abbvie-external/IR-MALDESI-MS/CAD/ArduinoMega.SLDPRT

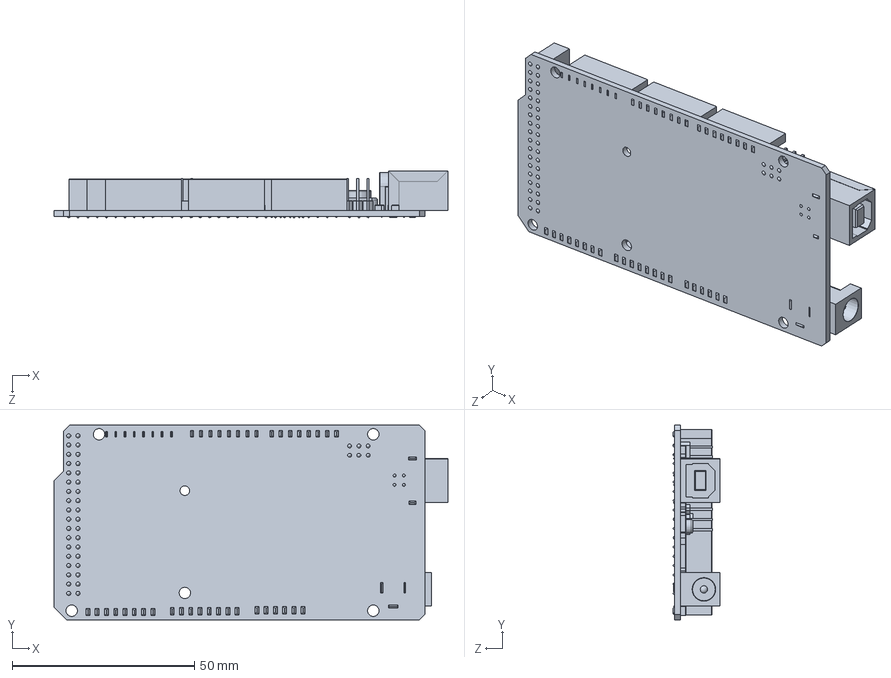
[picture p17: CAD file, 2023-03-30]
CAD/ArduinoMega.SLDPRT
107.9 x 53.4 x 13.0 mm
