abbvie-external/IR-MALDESI-MS/CAD/1332-0086.SLDPRT

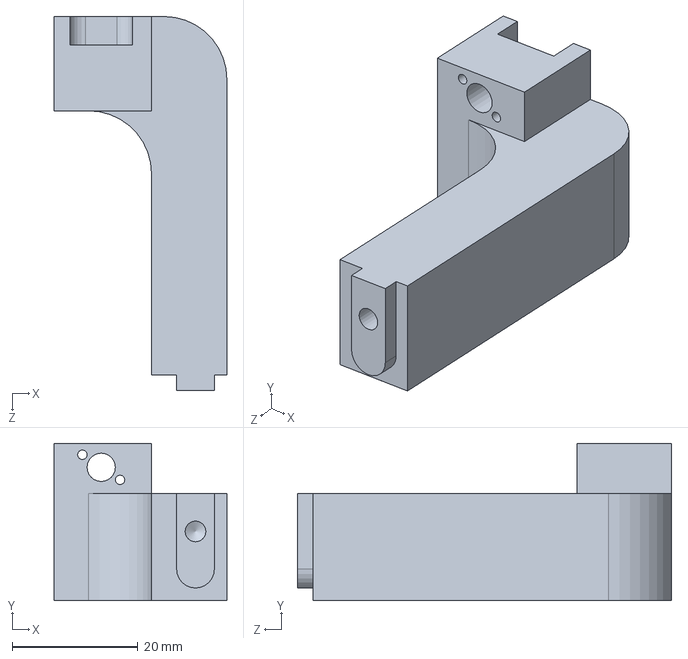
[picture p18: CAD file, 2023-03-30]
CAD/1332-0086.SLDPRT
27.5 x 25.0 x 59.5 mm
