abbvie-external/IR-MALDESI-MS/CAD/Axis 5 Wrist support simple.SLDPRT

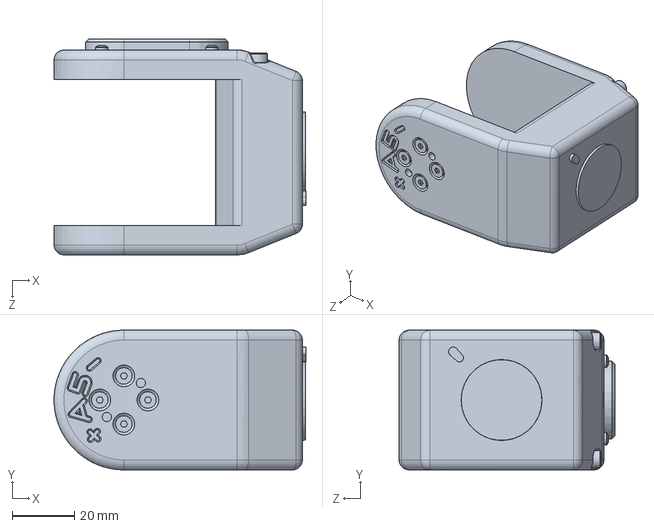
[picture p19: CAD file, 2023-03-30]
CAD/Axis 5 Wrist support simple.SLDPRT
81.1 x 45.0 x 69.5 mm
