abbvie-external/IR-MALDESI-MS/CAD/1332-0083.SLDPRT

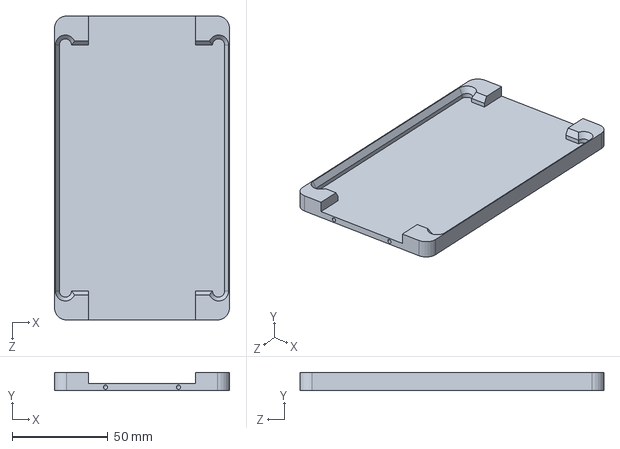
[picture p20: CAD file, 2023-03-30]
CAD/1332-0083.SLDPRT
91.4 x 9.53 x 158.8 mm
