abbvie-external/IR-MALDESI-MS/CAD/1332-0091.SLDPRT

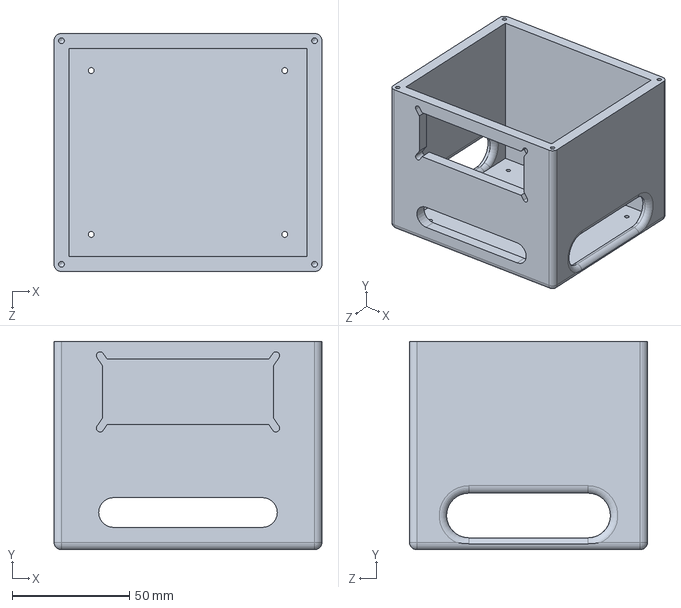
[picture p21: CAD file, 2023-03-30]
CAD/1332-0091.SLDPRT
114.3 x 88.9 x 101.6 mm
