abbvie-external/IR-MALDESI-MS/CAD/1332-0089.SLDPRT

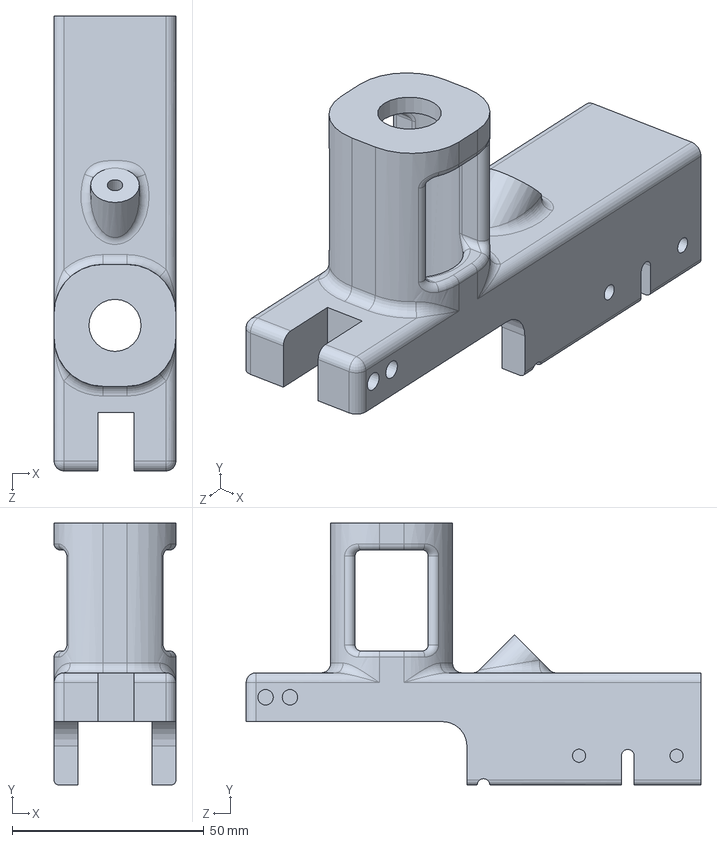
[picture p22: CAD file, 2023-03-30]
CAD/1332-0089.SLDPRT
31.8 x 68.3 x 118.5 mm
