abbvie-external/IR-MALDESI-MS/CAD/SM05V10.SLDPRT

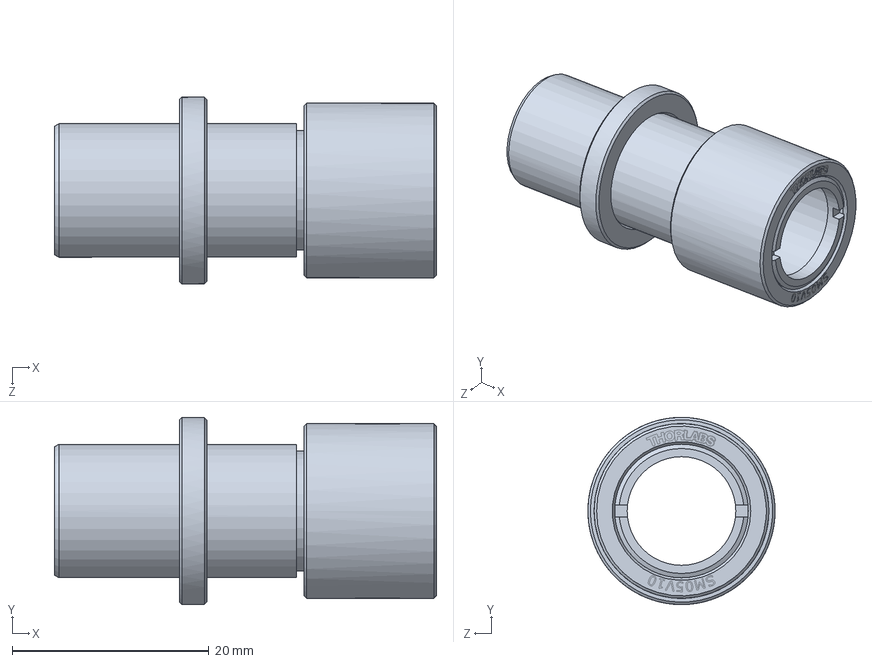
[picture p23: CAD file, 2023-03-30]
CAD/SM05V10.SLDPRT
38.9 x 19.0 x 19.1 mm
