abbvie-external/IR-MALDESI-MS/CAD/Meca Rail adjustable.SLDPRT

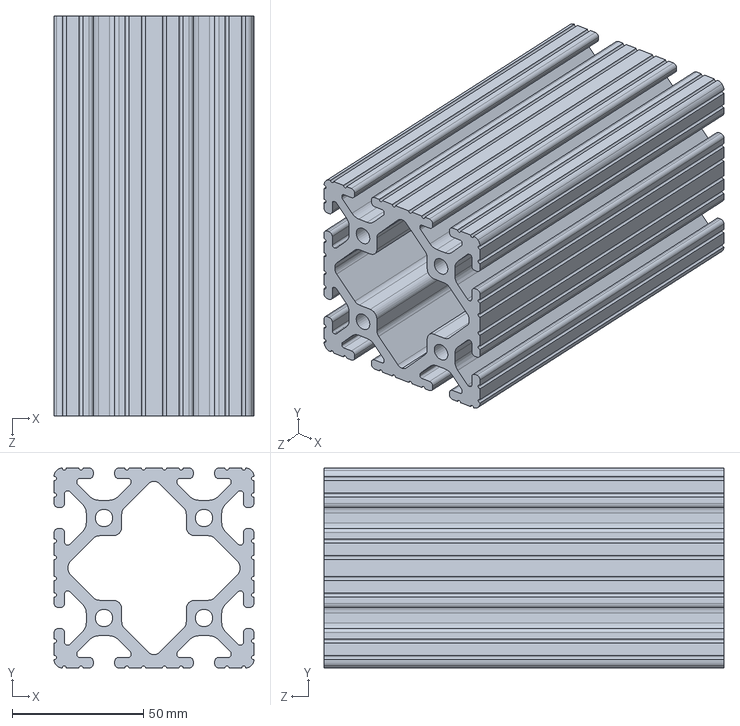
[picture p24: CAD file, 2023-03-30]
CAD/Meca Rail adjustable.SLDPRT
76.2 x 76.2 x 152.4 mm
