abbvie-external/IR-MALDESI-MS/CAD/Thermo Q Exactive HF.SLDPRT

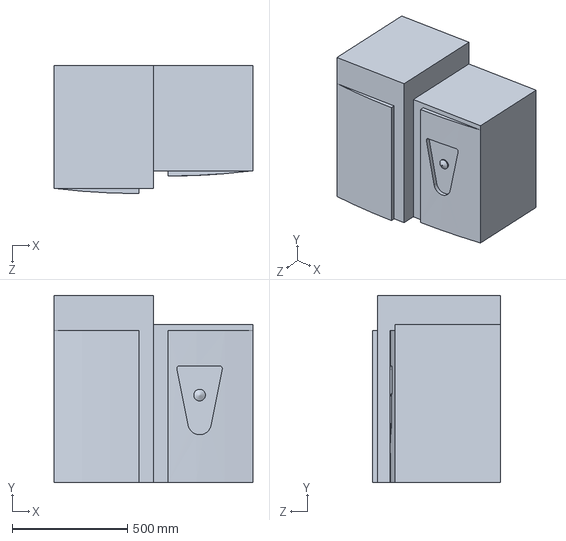
[picture p25: CAD file, 2023-03-30]
CAD/Thermo Q Exactive HF.SLDPRT
863.6 x 812.8 x 556.3 mm
