abbvie-external/IR-MALDESI-MS/CAD/U-MALDESI - Silica ESI Probe.SLDPRT

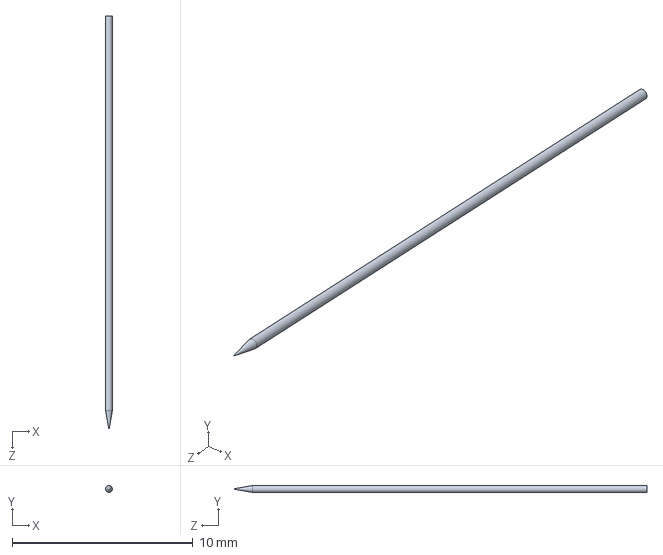
[picture p26: CAD file, 2023-03-30]
CAD/U-MALDESI - Silica ESI Probe.SLDPRT
0.381 x 0.381 x 22.9 mm
