abbvie-external/IR-MALDESI-MS/CAD/1332-0079.SLDPRT

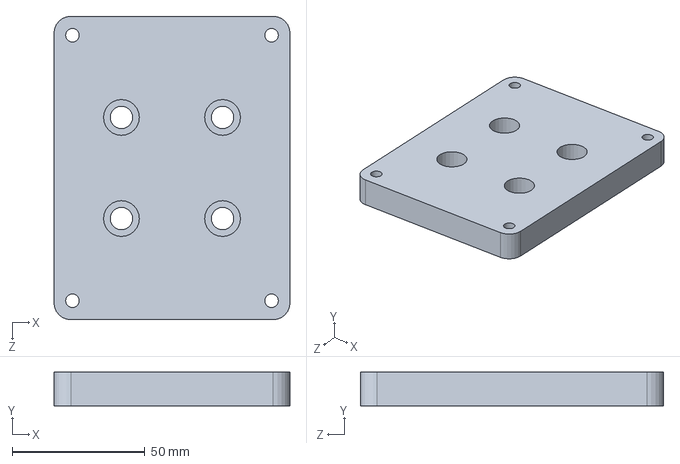
[picture p27: CAD file, 2023-03-30]
CAD/1332-0079.SLDPRT
88.9 x 12.7 x 114.3 mm
