abbvie-external/IR-MALDESI-MS/CAD/KCB05.SLDPRT

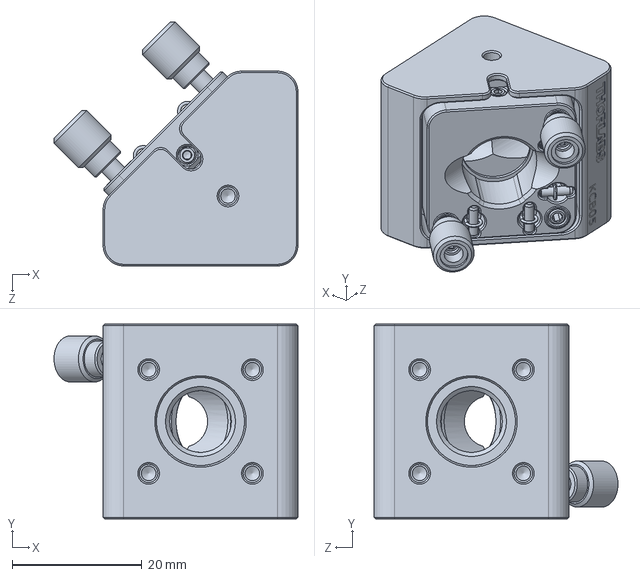
[picture p28: CAD file, 2023-03-30]
CAD/KCB05.SLDPRT
37.6 x 30.1 x 37.6 mm
