abbvie-external/IR-MALDESI-MS/CAD/DIN RAIL 35mm X 7.5mm.SLDPRT

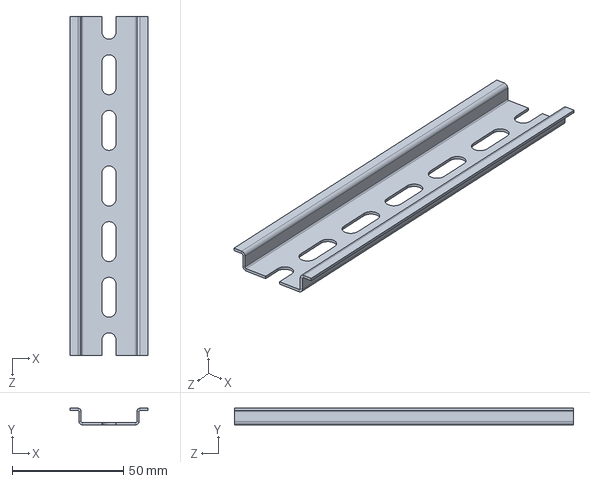
[picture p29: CAD file, 2023-03-30]
CAD/DIN RAIL 35mm X 7.5mm.SLDPRT
35.0 x 7.50 x 152.4 mm
