abbvie-external/IR-MALDESI-MS/CAD/SM05L30.SLDPRT

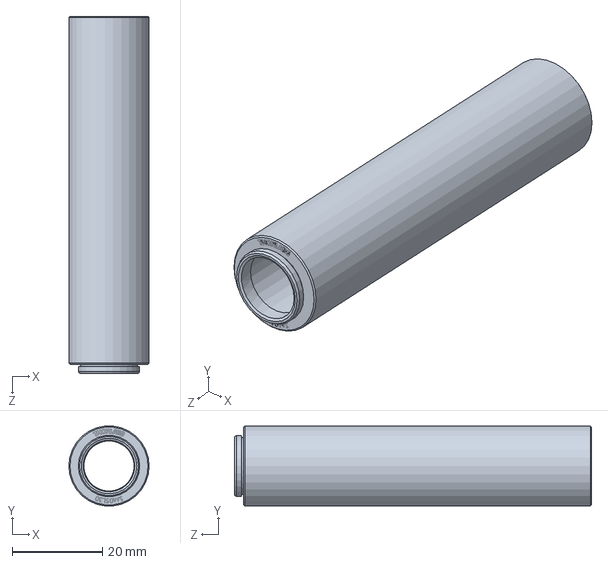
[picture p30: CAD file, 2023-03-30]
CAD/SM05L30.SLDPRT
17.8 x 17.7 x 79.0 mm
