abbvie-external/IR-MALDESI-MS/CAD/Meca500 Power Supply.SLDPRT

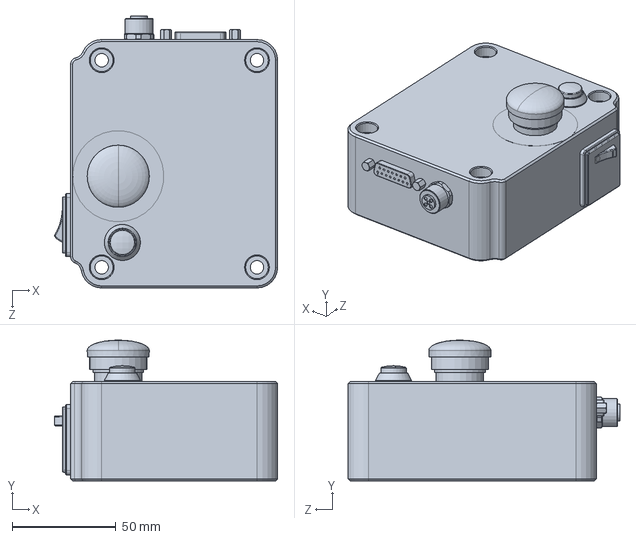
[picture p31: CAD file, 2023-03-30]
CAD/Meca500 Power Supply.SLDPRT
107.9 x 68.0 x 131.4 mm
