abbvie-external/IR-MALDESI-MS/CAD/1332-0093.SLDPRT

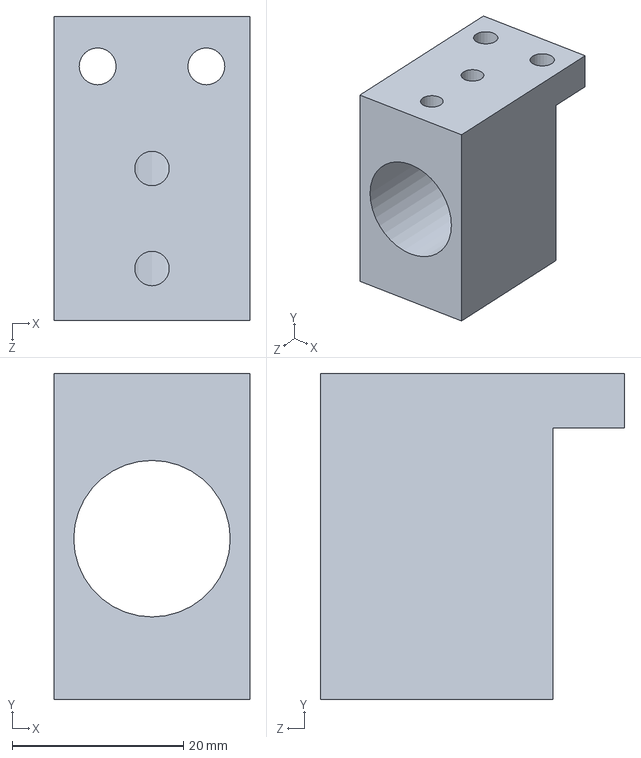
[picture p32: CAD file, 2023-03-30]
CAD/1332-0093.SLDPRT
22.9 x 38.1 x 35.6 mm
