abbvie-external/IR-MALDESI-MS/CAD/1332-0078.SLDPRT

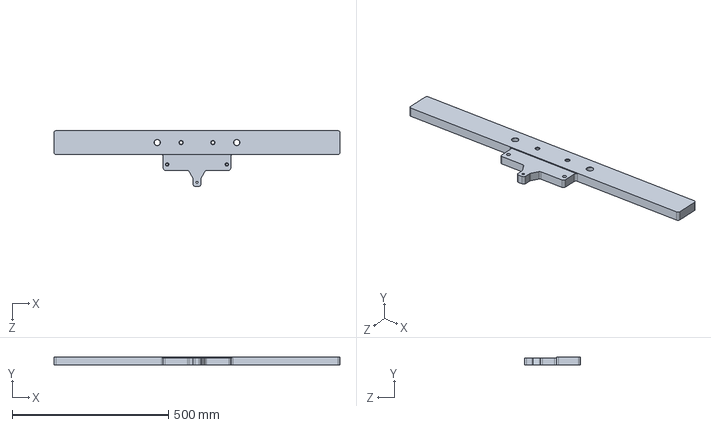
[picture p33: CAD file, 2023-03-30]
CAD/1332-0078.SLDPRT
914.4 x 25.4 x 177.8 mm
