abbvie-external/IR-MALDESI-MS/CAD/Tecan Genesis Workstation 100 - RoMa Gripper SBS Finger LEFT.SLDPRT

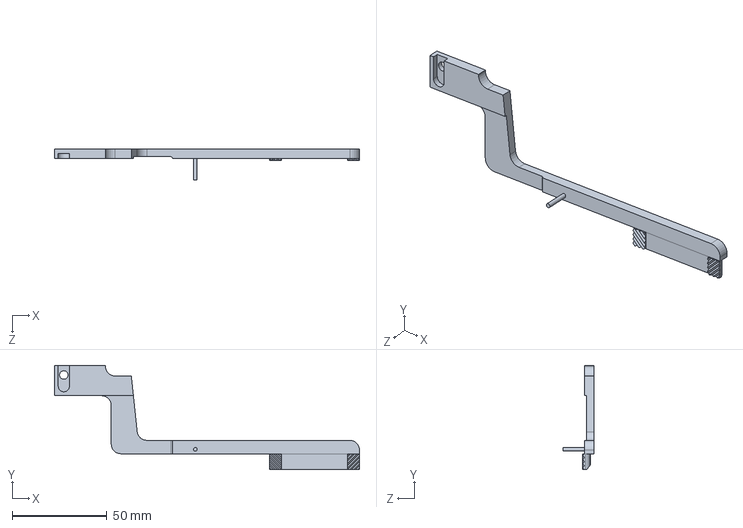
[picture p34: CAD file, 2023-03-30]
CAD/Tecan Genesis Workstation 100 - RoMa Gripper SBS Finger LEFT.SLDPRT
161.3 x 55.1 x 16.2 mm
