abbvie-external/IR-MALDESI-MS/CAD/Tecan Genesis Workstation 100 - RoMa Gripper SBS Finger RIGHT.SLDPRT

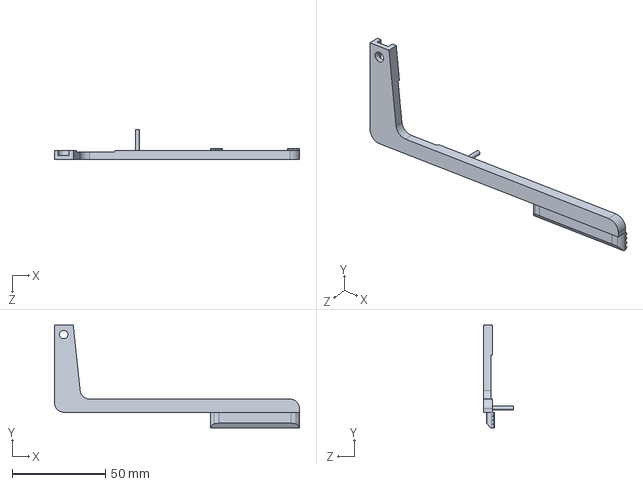
[picture p35: CAD file, 2023-03-30]
CAD/Tecan Genesis Workstation 100 - RoMa Gripper SBS Finger RIGHT.SLDPRT
131.3 x 55.1 x 16.2 mm
