abbvie-external/IR-MALDESI-MS/CAD/Gripper.SLDPRT

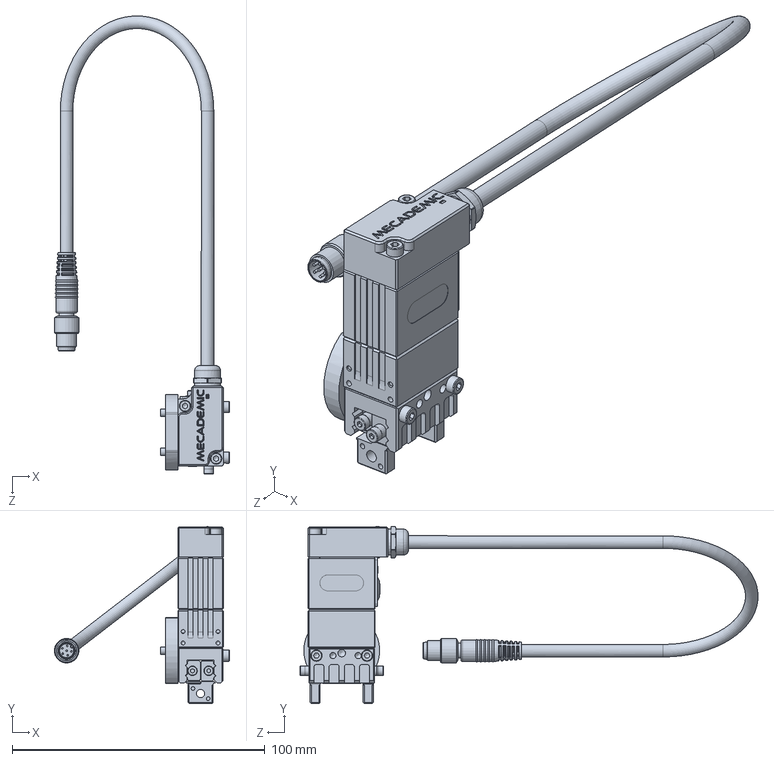
[picture p36: CAD file, 2023-03-30]
CAD/Gripper.SLDPRT
69.2 x 70.1 x 181.1 mm
