abbvie-external/IR-MALDESI-MS/CAD/1332-0081.SLDPRT

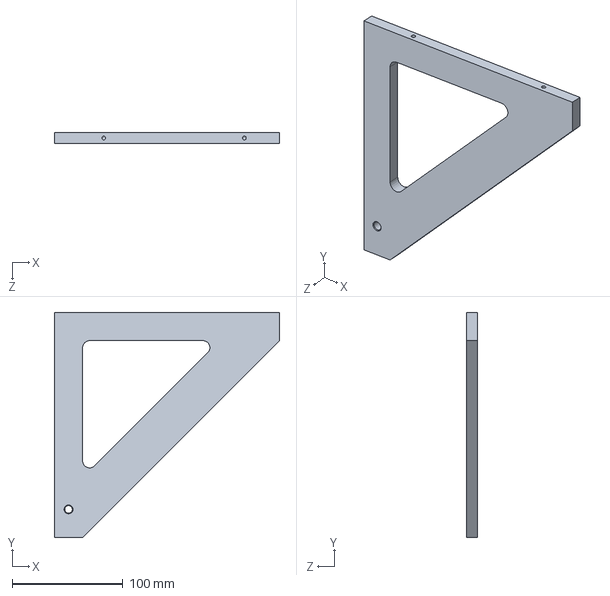
[picture p37: CAD file, 2023-03-30]
CAD/1332-0081.SLDPRT
203.2 x 203.2 x 9.53 mm
