abbvie-external/IR-MALDESI-MS/CAD/1332-0082.SLDPRT

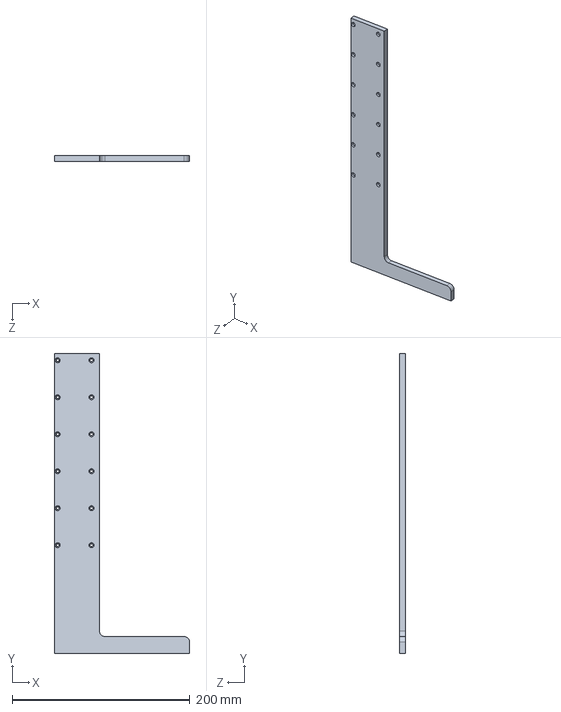
[picture p38: CAD file, 2023-03-30]
CAD/1332-0082.SLDPRT
152.4 x 337.8 x 6.35 mm
