abbvie-external/IR-MALDESI-MS/CAD/Axis 2 Hip support simple.SLDPRT

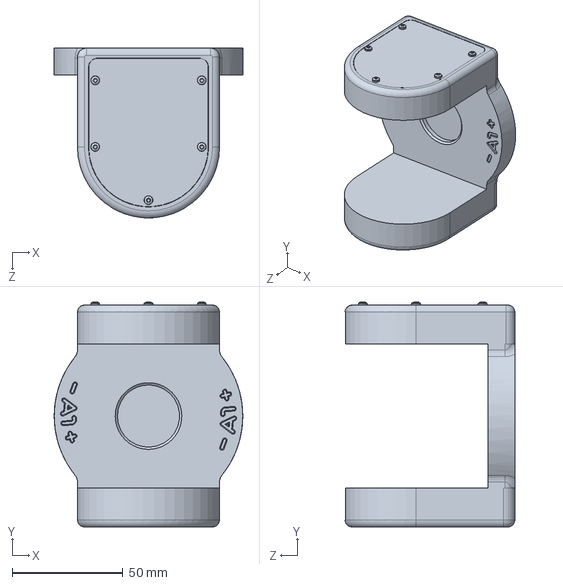
[picture p39: CAD file, 2023-03-30]
CAD/Axis 2 Hip support simple.SLDPRT
85.0 x 101.4 x 76.5 mm
