abbvie-external/IR-MALDESI-MS/CAD/Axis 6 Wrist simple.SLDPRT

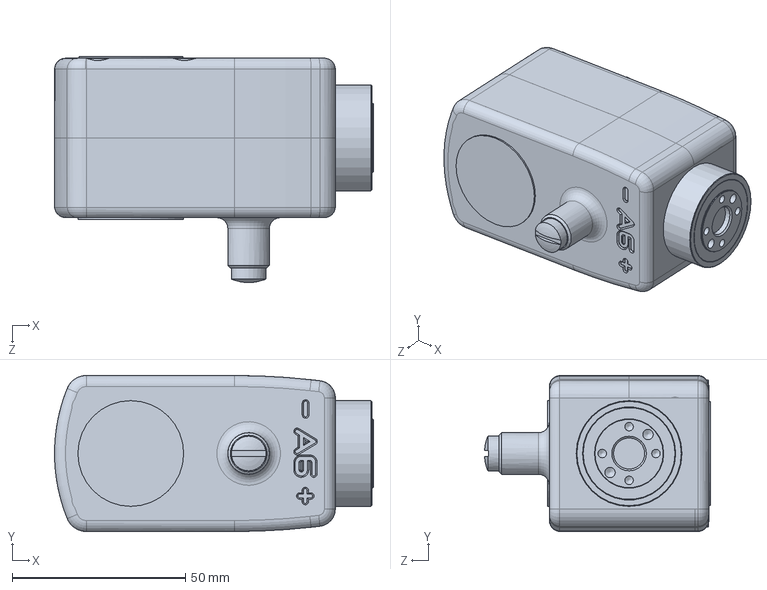
[picture p40: CAD file, 2023-03-30]
CAD/Axis 6 Wrist simple.SLDPRT
92.0 x 45.0 x 65.2 mm
