abbvie-external/IR-MALDESI-MS/CAD/1332-0092.SLDPRT

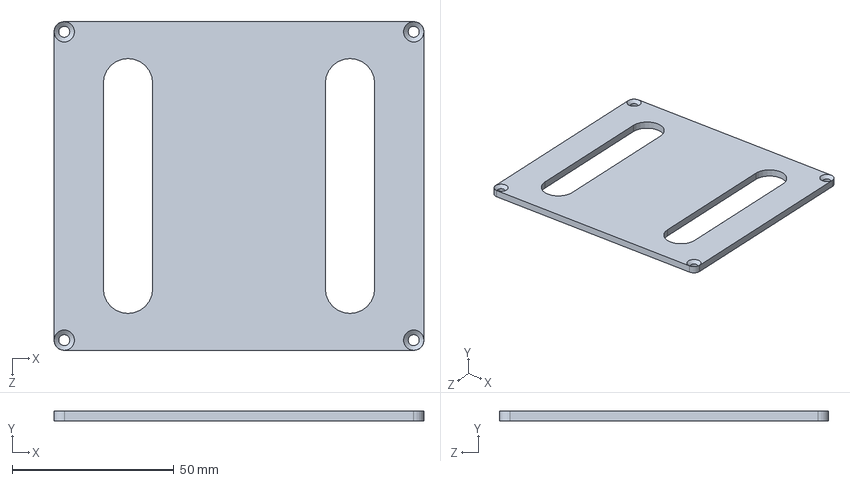
[picture p41: CAD file, 2023-03-30]
CAD/1332-0092.SLDPRT
114.3 x 3.17 x 101.6 mm
