abbvie-external/IR-MALDESI-MS/CAD/1332-0031.SLDPRT

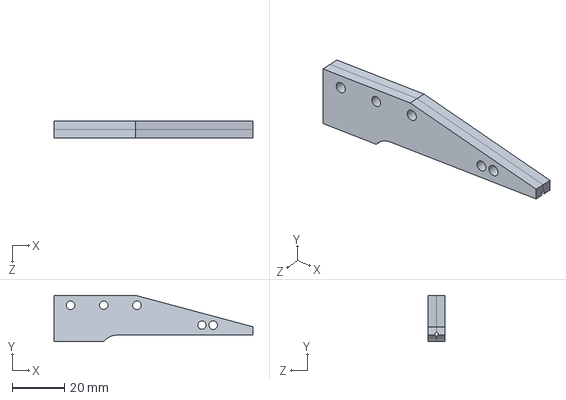
[picture p42: CAD file, 2023-03-30]
CAD/1332-0031.SLDPRT
76.2 x 17.8 x 6.35 mm
